dg3vw/Trekkie_Addon/pics/PXL_20250307_085014307.jpg

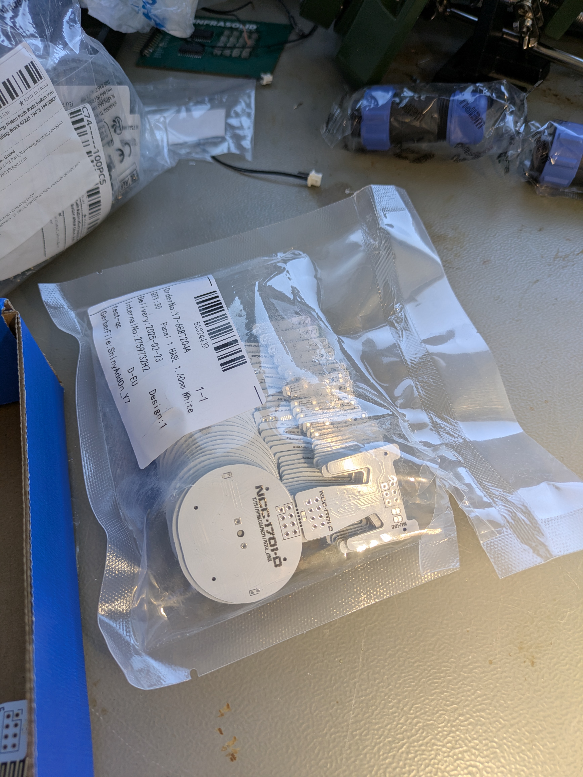
pics/PXL_20250307_085014307.jpg
