dg3vw/Trekkie_Addon/pics/PXL_20250307_085021719.jpg

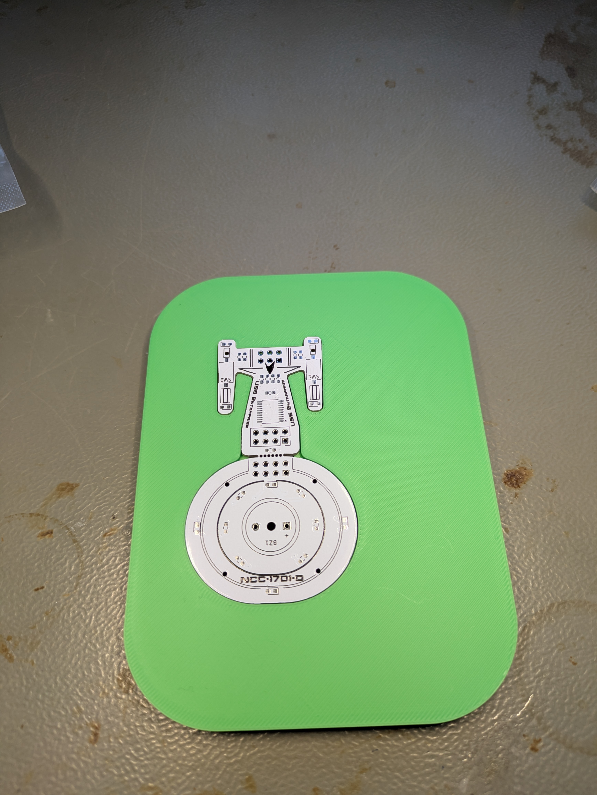
pics/PXL_20250307_085021719.jpg
