dg3vw/Trekkie_Addon/pics/PXL_20250307_085250391.jpg

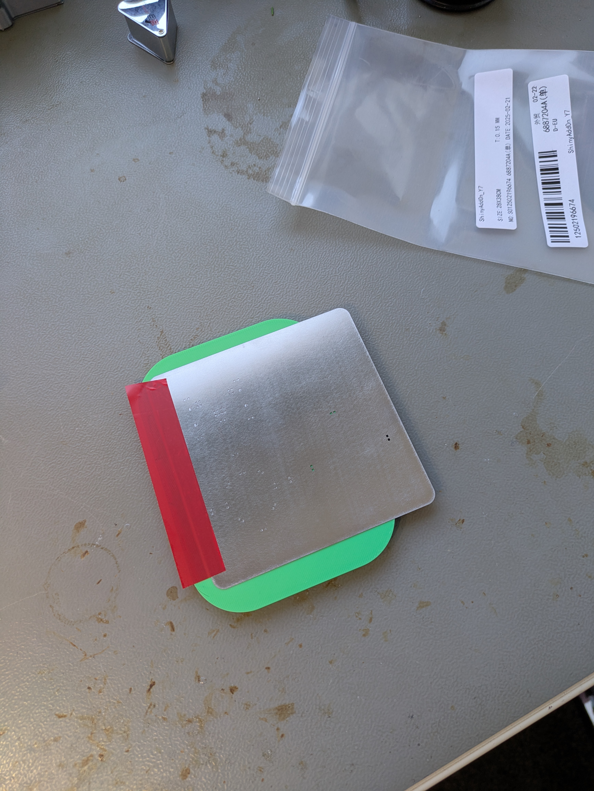
pics/PXL_20250307_085250391.jpg
