dg3vw/Trekkie_Addon/pics/PXL_20250307_085929696.jpg

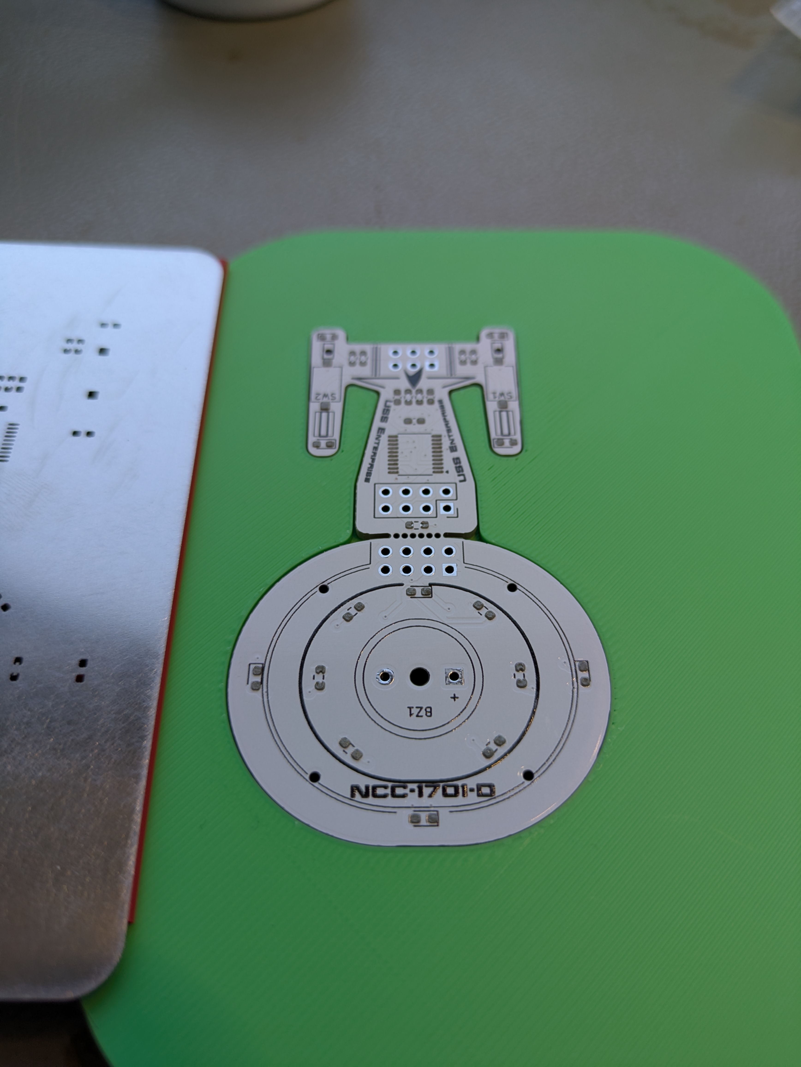
pics/PXL_20250307_085929696.jpg
