dg3vw/Trekkie_Addon/pics/PXL_20250307_085942884.jpg

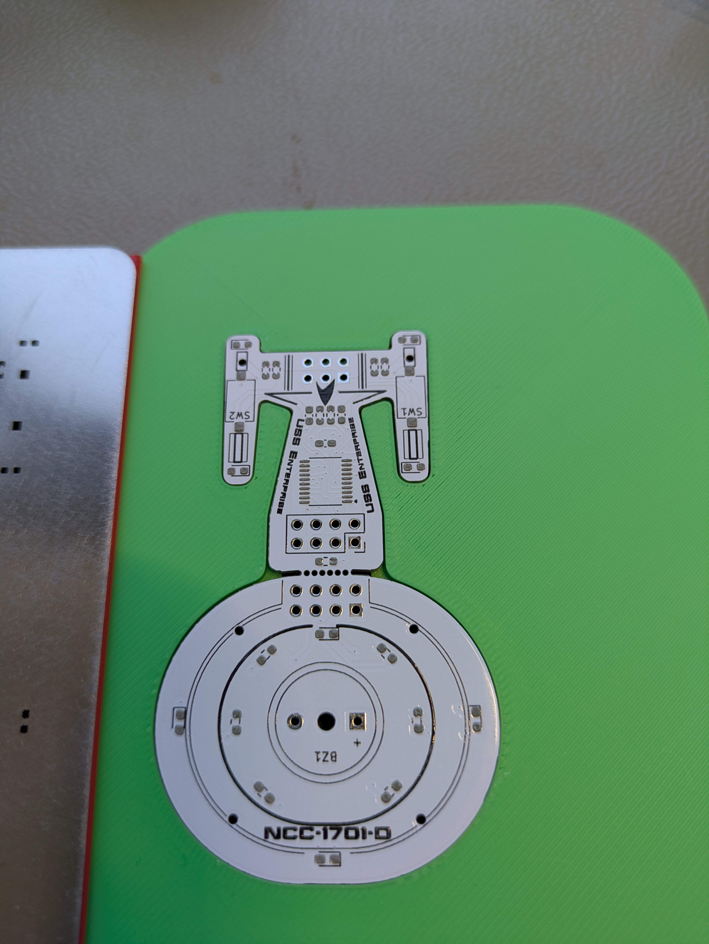
pics/PXL_20250307_085942884.jpg
