dg3vw/Trekkie_Addon/pics/PXL_20250307_090016560.jpg

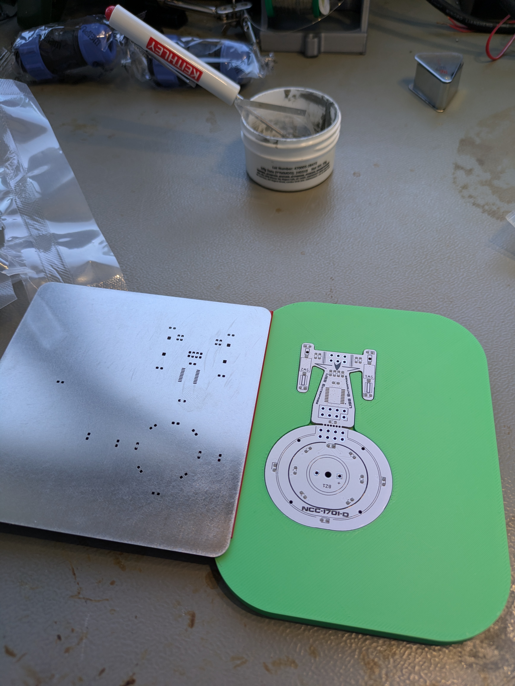
pics/PXL_20250307_090016560.jpg
