dg3vw/Trekkie_Addon/pics/PXL_20250307_103104777.jpg

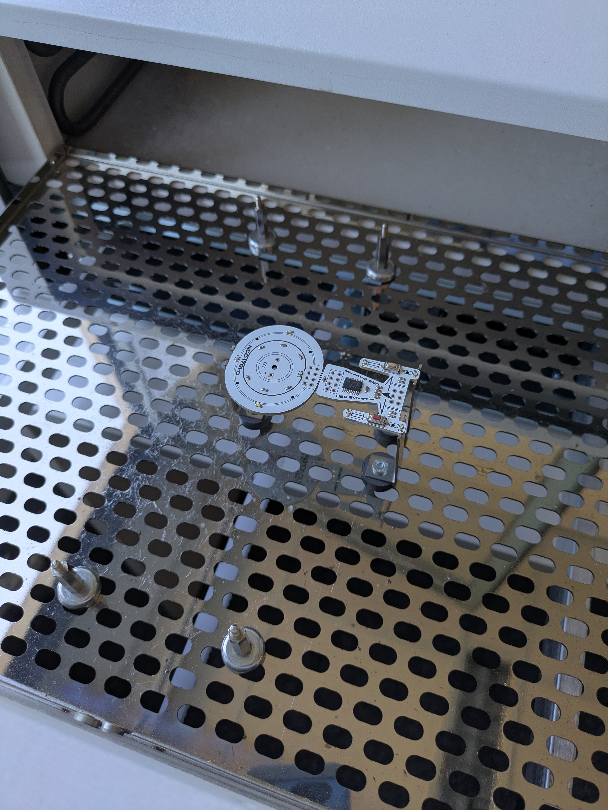
pics/PXL_20250307_103104777.jpg
