dg3vw/Trekkie_Addon/pics/PXL_20250307_114815561.jpg

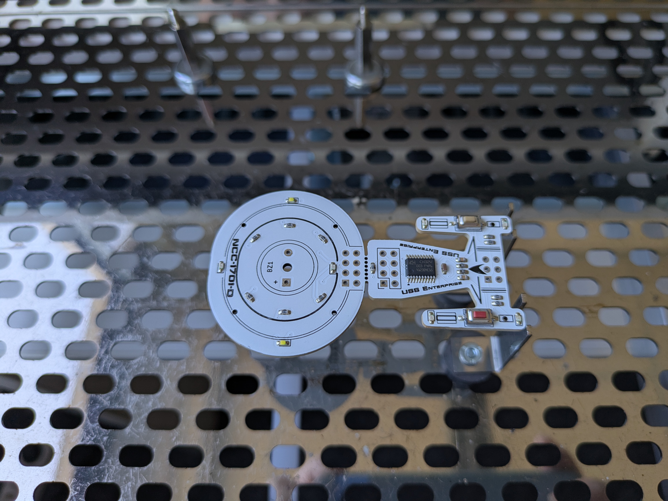
pics/PXL_20250307_114815561.jpg
