dg3vw/Trekkie_Addon/pics/PXL_20250307_121946914.jpg

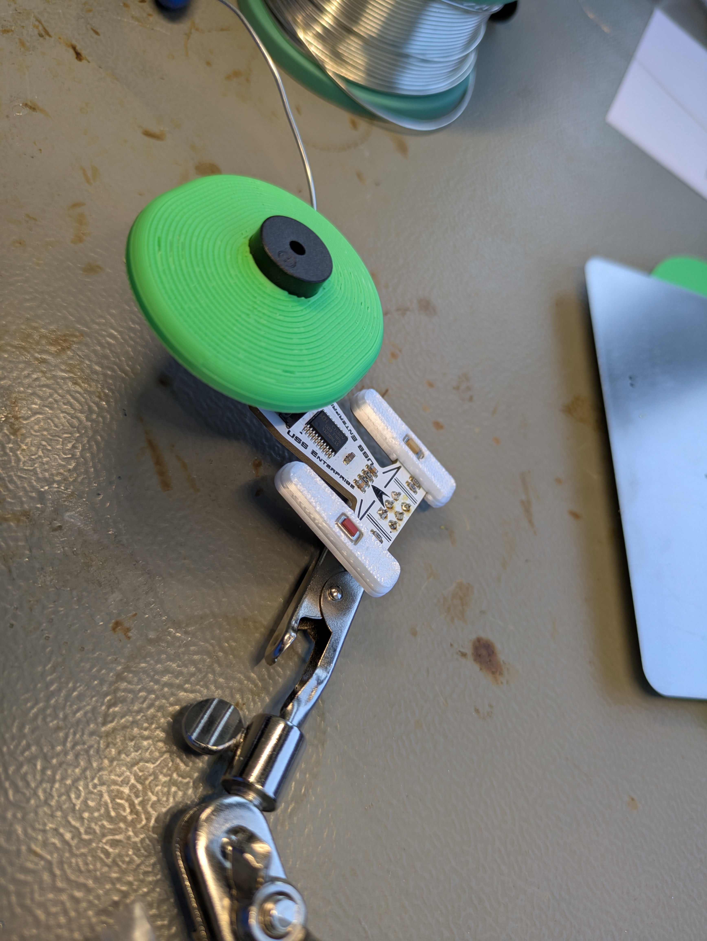
pics/PXL_20250307_121946914.jpg
