dg3vw/Trekkie_Addon/pics/PXL_20250310_173153761.jpg

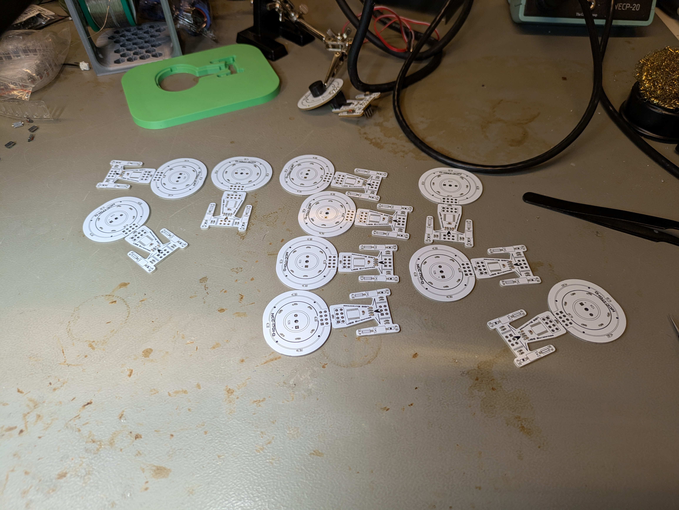
pics/PXL_20250310_173153761.jpg
