dg3vw/Trekkie_Addon/pics/PXL_20250310_173612652.jpg

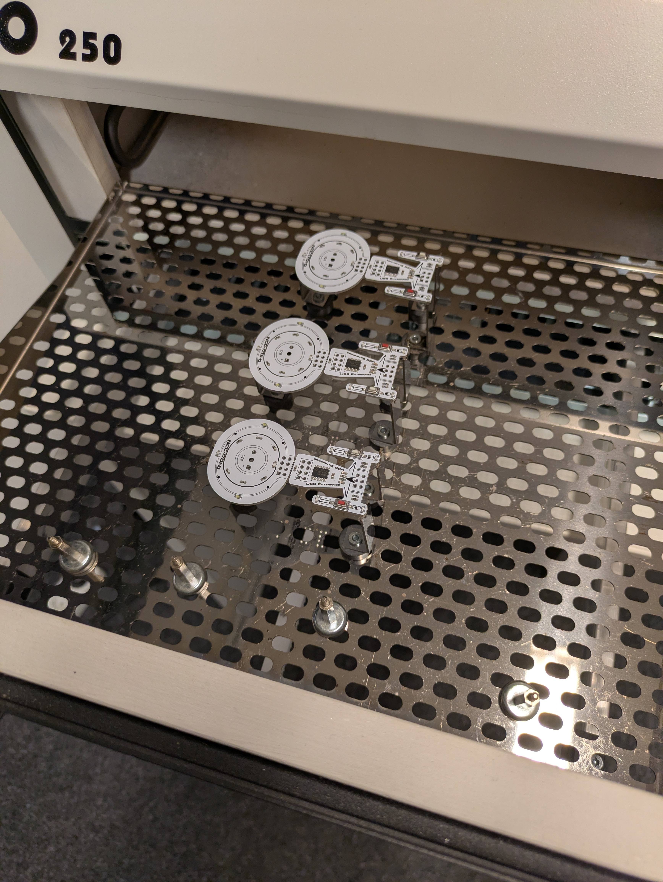
pics/PXL_20250310_173612652.jpg
