dg3vw/Trekkie_Addon/pics/PXL_20250310_182050628.jpg

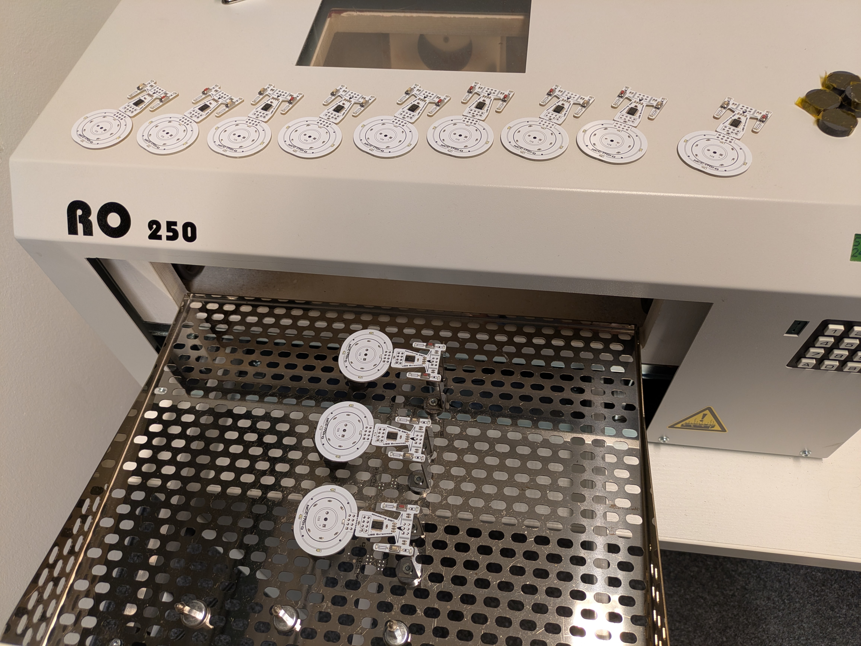
pics/PXL_20250310_182050628.jpg
