dg3vw/Trekkie_Addon/pics/PXL_20250314_204145882.jpg

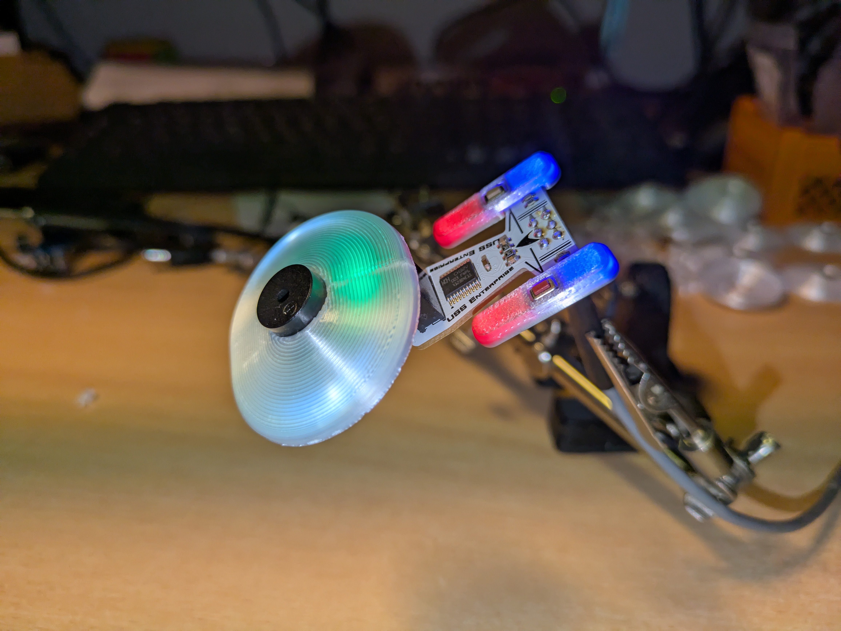
pics/PXL_20250314_204145882.jpg
