dg3vw/Trekkie_Addon/pics/PXL_20250314_204237018.jpg

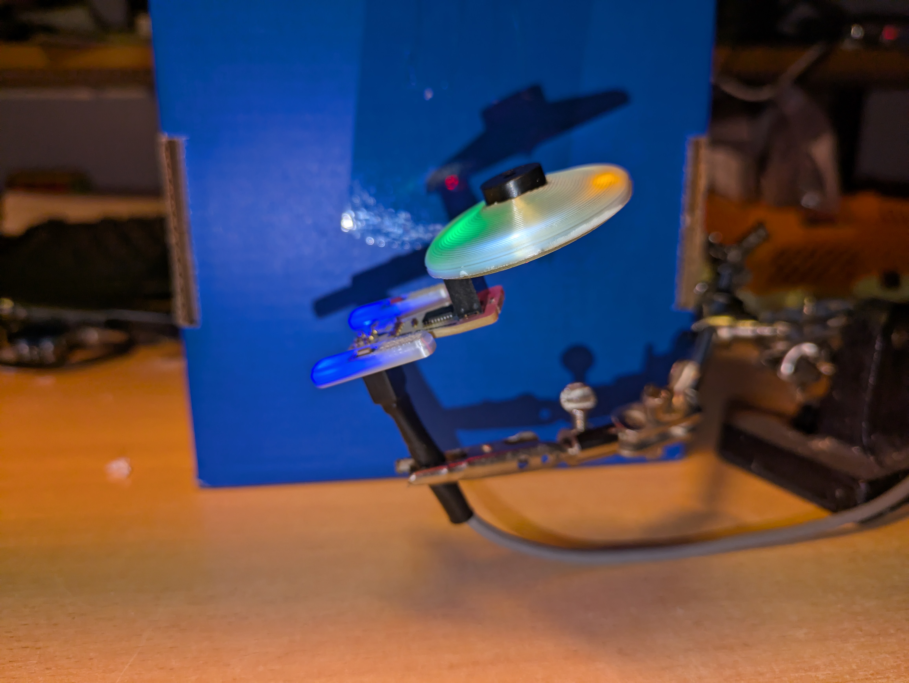
pics/PXL_20250314_204237018.jpg
