dg3vw/Trekkie_Addon/pics/PXL_20250314_204246564.MP.jpg

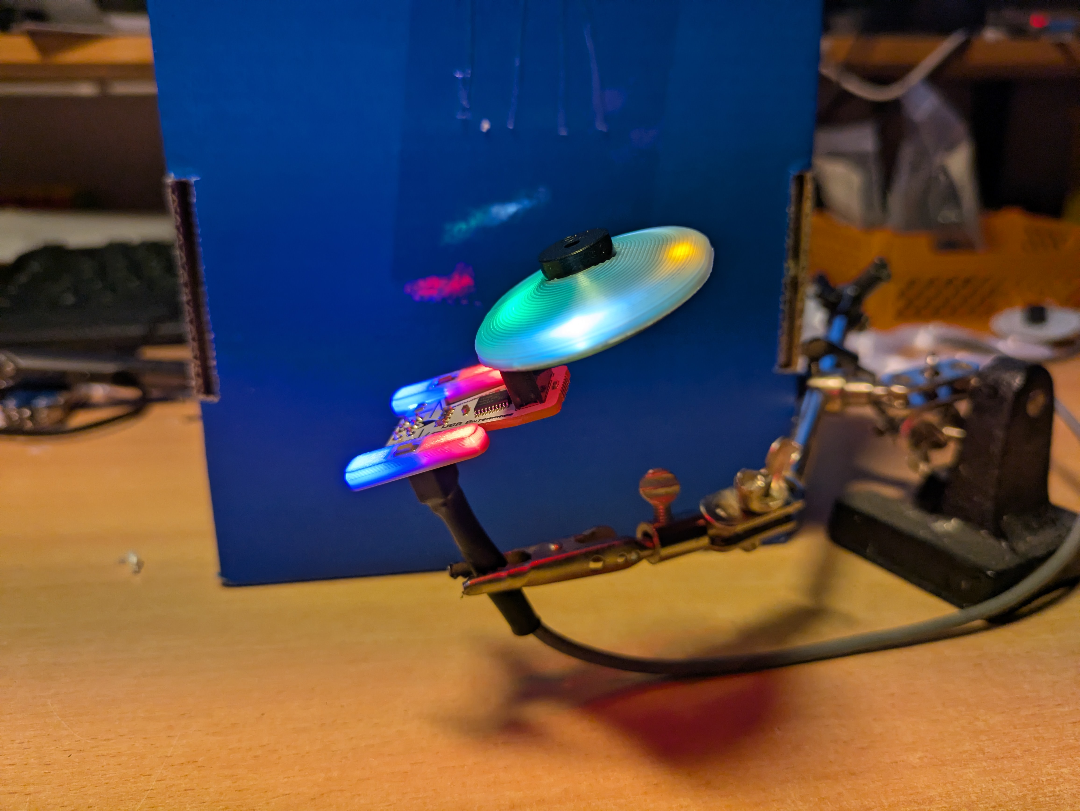
pics/PXL_20250314_204246564.MP.jpg
