dg3vw/Trekkie_Addon/pics/PXL_20250314_204249380.MP~2.jpg

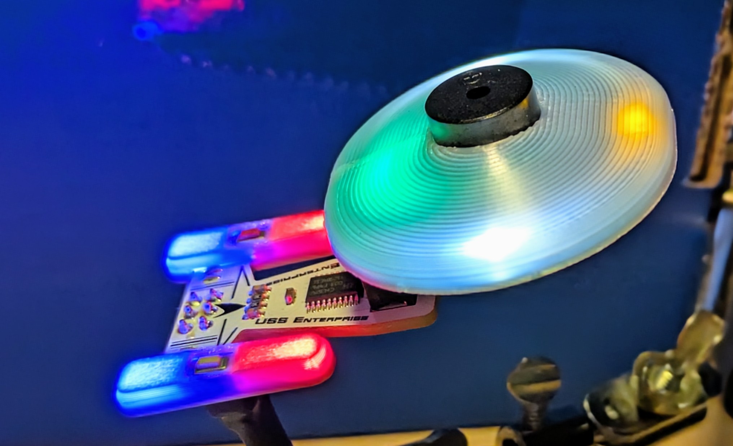
pics/PXL_20250314_204249380.MP~2.jpg
