dg3vw/Trekkie_Addon/pics/PXL_20250314_204252658.MP~2.jpg

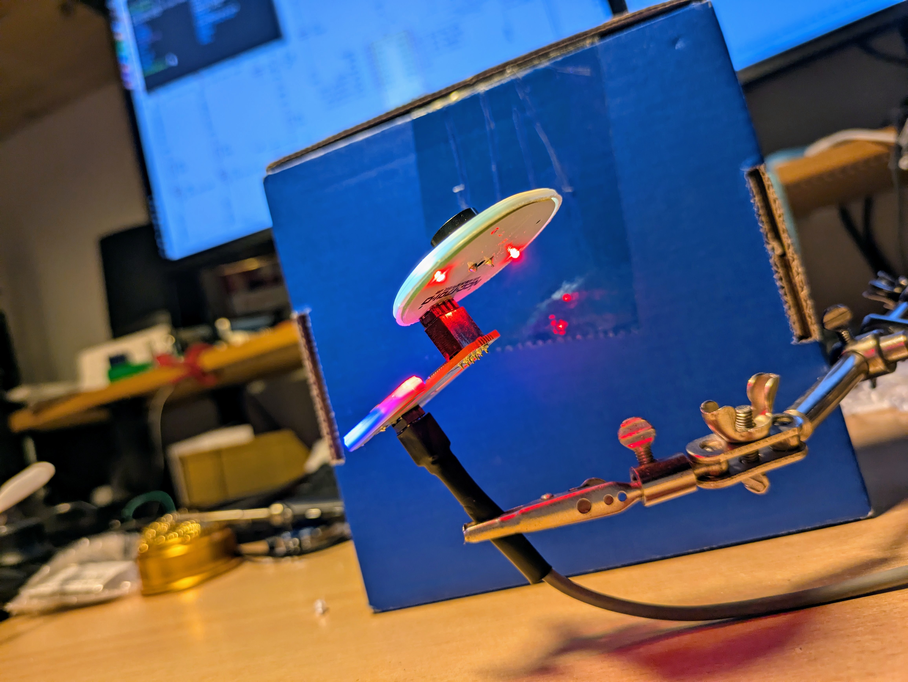
pics/PXL_20250314_204252658.MP~2.jpg
